aumouvantsillage/midi314/software/pcd8544/src/terminus6x12.rs

use font::*;

pub const WIDTH : usize = 6;

pub const HEIGHT : usize = 12;

pub const CHARS : usize = 892;

pub static BITMAP : [u8 ; CHARS * HEIGHT] = [
//   0 $00 'char0'
//	width 6, bbx 0, bby -2, bbw 6, bbh 12
	________,
	________,
	XX_XX___,
	X___X___,
	________,
	X___X___,
	X___X___,
	________,
	X___X___,
	XX_XX___,
	________,
	________,
//  32 $20 'space'
//	width 6, bbx 0, bby -2, bbw 6, bbh 12
	________,
	________,
	________,
	________,
	________,
	________,
	________,
	________,
	________,
	________,
	________,
	________,
//  33 $21 'exclam'
//	width 6, bbx 0, bby -2, bbw 6, bbh 12
	________,
	________,
	__X_____,
	__X_____,
	__X_____,
	__X_____,
	__X_____,
	________,
	__X_____,
	__X_____,
	________,
	________,
//  34 $22 'quotedbl'
//	width 6, bbx 0, bby -2, bbw 6, bbh 12
	________,
	_X_X____,
	_X_X____,
	_X_X____,
	________,
	________,
	________,
	________,
	________,
	________,
	________,
	________,
//  35 $23 'numbersign'
//	width 6, bbx 0, bby -2, bbw 6, bbh 12
	________,
	________,
	_X_X____,
	_X_X____,
	XXXXX___,
	_X_X____,
	_X_X____,
	XXXXX___,
	_X_X____,
	_X_X____,
	________,
	________,
//  36 $24 'dollar'
//	width 6, bbx 0, bby -2, bbw 6, bbh 12
	________,
	________,
	__X_____,
	_XXX____,
	X_X_X___,
	X_X_____,
	_XXX____,
	__X_X___,
	X_X_X___,
	_XXX____,
	__X_____,
	________,
//  37 $25 'percent'
//	width 6, bbx 0, bby -2, bbw 6, bbh 12
	________,
	________,
	_X__X___,
	X_X_X___,
	_X_X____,
	___X____,
	__X_____,
	__X_X___,
	_X_X_X__,
	_X__X___,
	________,
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
//	width 6, bbx 0, bby -2, bbw 6, bbh 12
	________,
	________,
	__X_X___,
	_X_X____,
	X___X___,
	X___X___,
	X___X___,
	X___X___,
	X___X___,
	_XXXX___,
	____X___,
	_XXX____,
// 8192 $2000 'uni2000'
//	width 6, bbx 0, bby -2, bbw 6, bbh 12
	________,
	________,
	________,
	________,
	________,
	________,
	________,
	________,
	________,
	________,
	________,
	________,
// 8193 $2001 'uni2001'
//	width 6, bbx 0, bby -2, bbw 6, bbh 12
	________,
	________,
	________,
	________,
	________,
	________,
	________,
	________,
	________,
	________,
	________,
	________,
// 8194 $2002 'enspace'
//	width 6, bbx 0, bby -2, bbw 6, bbh 12
	________,
	________,
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
