aumouvantsillage/midi314/software/pcd8544/src/font.rs

pub const ________ : u8 = 0x00;
pub const _______X : u8 = 0x01;
pub const ______X_ : u8 = 0x02;
pub const ______XX : u8 = 0x03;
pub const _____X__ : u8 = 0x04;
pub const _____X_X : u8 = 0x05;
pub const _____XX_ : u8 = 0x06;
pub const _____XXX : u8 = 0x07;
pub const ____X___ : u8 = 0x08;
pub const ____X__X : u8 = 0x09;
pub const ____X_X_ : u8 = 0x0A;
pub const ____X_XX : u8 = 0x0B;
pub const ____XX__ : u8 = 0x0C;
pub const ____XX_X : u8 = 0x0D;
pub const ____XXX_ : u8 = 0x0E;
pub const ____XXXX : u8 = 0x0F;
pub const ___X____ : u8 = 0x10;
pub const ___X___X : u8 = 0x11;
pub const ___X__X_ : u8 = 0x12;
pub const ___X__XX : u8 = 0x13;
pub const ___X_X__ : u8 = 0x14;
pub const ___X_X_X : u8 = 0x15;
pub const ___X_XX_ : u8 = 0x16;
pub const ___X_XXX : u8 = 0x17;
pub const ___XX___ : u8 = 0x18;
pub const ___XX__X : u8 = 0x19;
pub const ___XX_X_ : u8 = 0x1A;
pub const ___XX_XX : u8 = 0x1B;
pub const ___XXX__ : u8 = 0x1C;
pub const ___XXX_X : u8 = 0x1D;
pub const ___XXXX_ : u8 = 0x1E;
pub const ___XXXXX : u8 = 0x1F;
pub const __X_____ : u8 = 0x20;
pub const __X____X : u8 = 0x21;
pub const __X___X_ : u8 = 0x22;
pub const __X___XX : u8 = 0x23;
pub const __X__X__ : u8 = 0x24;
pub const __X__X_X : u8 = 0x25;
pub const __X__XX_ : u8 = 0x26;
pub const __X__XXX : u8 = 0x27;
pub const __X_X___ : u8 = 0x28;
pub const __X_X__X : u8 = 0x29;
pub const __X_X_X_ : u8 = 0x2A;
pub const __X_X_XX : u8 = 0x2B;
pub const __X_XX__ : u8 = 0x2C;
pub const __X_XX_X : u8 = 0x2D;
pub const __X_XXX_ : u8 = 0x2E;
pub const __X_XXXX : u8 = 0x2F;
pub const __XX____ : u8 = 0x30;
pub const __XX___X : u8 = 0x31;
pub const __XX__X_ : u8 = 0x32;
pub const __XX__XX : u8 = 0x33;
pub const __XX_X__ : u8 = 0x34;
pub const __XX_X_X : u8 = 0x35;
pub const __XX_XX_ : u8 = 0x36;
pub const __XX_XXX : u8 = 0x37;
pub const __XXX___ : u8 = 0x38;
pub const __XXX__X : u8 = 0x39;
pub const __XXX_X_ : u8 = 0x3A;
pub const __XXX_XX : u8 = 0x3B;
pub const __XXXX__ : u8 = 0x3C;
pub const __XXXX_X : u8 = 0x3D;
pub const __XXXXX_ : u8 = 0x3E;
pub const __XXXXXX : u8 = 0x3F;
pub const _X______ : u8 = 0x40;
pub const _X_____X : u8 = 0x41;
pub const _X____X_ : u8 = 0x42;
pub const _X____XX : u8 = 0x43;
pub const _X___X__ : u8 = 0x44;
pub const _X___X_X : u8 = 0x45;
pub const _X___XX_ : u8 = 0x46;
pub const _X___XXX : u8 = 0x47;
pub const _X__X___ : u8 = 0x48;
pub const _X__X__X : u8 = 0x49;
pub const _X__X_X_ : u8 = 0x4A;
pub const _X__X_XX : u8 = 0x4B;
pub const _X__XX__ : u8 = 0x4C;
pub const _X__XX_X : u8 = 0x4D;
pub const _X__XXX_ : u8 = 0x4E;
pub const _X__XXXX : u8 = 0x4F;
pub const _X_X____ : u8 = 0x50;
pub const _X_X___X : u8 = 0x51;
pub const _X_X__X_ : u8 = 0x52;
pub const _X_X__XX : u8 = 0x53;
pub const _X_X_X__ : u8 = 0x54;
pub const _X_X_X_X : u8 = 0x55;
pub const _X_X_XX_ : u8 = 0x56;
pub const _X_X_XXX : u8 = 0x57;
pub const _X_XX___ : u8 = 0x58;
pub const _X_XX__X : u8 = 0x59;
pub const _X_XX_X_ : u8 = 0x5A;
pub const _X_XX_XX : u8 = 0x5B;
pub const _X_XXX__ : u8 = 0x5C;
pub const _X_XXX_X : u8 = 0x5D;
pub const _X_XXXX_ : u8 = 0x5E;
pub const _X_XXXXX : u8 = 0x5F;
pub const _XX_____ : u8 = 0x60;
pub const _XX____X : u8 = 0x61;
pub const _XX___X_ : u8 = 0x62;
pub const _XX___XX : u8 = 0x63;
pub const _XX__X__ : u8 = 0x64;
pub const _XX__X_X : u8 = 0x65;
pub const _XX__XX_ : u8 = 0x66;
pub const _XX__XXX : u8 = 0x67;
pub const _XX_X___ : u8 = 0x68;
pub const _XX_X__X : u8 = 0x69;
pub const _XX_X_X_ : u8 = 0x6A;
pub const _XX_X_XX : u8 = 0x6B;
pub const _XX_XX__ : u8 = 0x6C;
pub const _XX_XX_X : u8 = 0x6D;
pub const _XX_XXX_ : u8 = 0x6E;
pub const _XX_XXXX : u8 = 0x6F;
pub const _XXX____ : u8 = 0x70;
pub const _XXX___X : u8 = 0x71;
pub const _XXX__X_ : u8 = 0x72;
pub const _XXX__XX : u8 = 0x73;
pub const _XXX_X__ : u8 = 0x74;
pub const _XXX_X_X : u8 = 0x75;
pub const _XXX_XX_ : u8 = 0x76;
pub const _XXX_XXX : u8 = 0x77;
pub const _XXXX___ : u8 = 0x78;
pub const _XXXX__X : u8 = 0x79;
pub const _XXXX_X_ : u8 = 0x7A;
pub const _XXXX_XX : u8 = 0x7B;
pub const _XXXXX__ : u8 = 0x7C;
pub const _XXXXX_X : u8 = 0x7D;
pub const _XXXXXX_ : u8 = 0x7E;
pub const _XXXXXXX : u8 = 0x7F;
pub const X_______ : u8 = 0x80;
pub const X______X : u8 = 0x81;
pub const X_____X_ : u8 = 0x82;
pub const X_____XX : u8 = 0x83;
pub const X____X__ : u8 = 0x84;
pub const X____X_X : u8 = 0x85;
pub const X____XX_ : u8 = 0x86;
pub const X____XXX : u8 = 0x87;
pub const X___X___ : u8 = 0x88;
pub const X___X__X : u8 = 0x89;
pub const X___X_X_ : u8 = 0x8A;
pub const X___X_XX : u8 = 0x8B;
pub const X___XX__ : u8 = 0x8C;
pub const X___XX_X : u8 = 0x8D;
pub const X___XXX_ : u8 = 0x8E;
pub const X___XXXX : u8 = 0x8F;
pub const X__X____ : u8 = 0x90;
pub const X__X___X : u8 = 0x91;
pub const X__X__X_ : u8 = 0x92;
pub const X__X__XX : u8 = 0x93;
pub const X__X_X__ : u8 = 0x94;
pub const X__X_X_X : u8 = 0x95;
pub const X__X_XX_ : u8 = 0x96;
pub const X__X_XXX : u8 = 0x97;
pub const X__XX___ : u8 = 0x98;
pub const X__XX__X : u8 = 0x99;
pub const X__XX_X_ : u8 = 0x9A;
pub const X__XX_XX : u8 = 0x9B;
pub const X__XXX__ : u8 = 0x9C;
pub const X__XXX_X : u8 = 0x9D;
pub const X__XXXX_ : u8 = 0x9E;
pub const X__XXXXX : u8 = 0x9F;
pub const X_X_____ : u8 = 0xA0;
pub const X_X____X : u8 = 0xA1;
pub const X_X___X_ : u8 = 0xA2;
pub const X_X___XX : u8 = 0xA3;
pub const X_X__X__ : u8 = 0xA4;
pub const X_X__X_X : u8 = 0xA5;
pub const X_X__XX_ : u8 = 0xA6;
pub const X_X__XXX : u8 = 0xA7;
pub const X_X_X___ : u8 = 0xA8;
pub const X_X_X__X : u8 = 0xA9;
pub const X_X_X_X_ : u8 = 0xAA;
pub const X_X_X_XX : u8 = 0xAB;
pub const X_X_XX__ : u8 = 0xAC;
pub const X_X_XX_X : u8 = 0xAD;
pub const X_X_XXX_ : u8 = 0xAE;
pub const X_X_XXXX : u8 = 0xAF;
pub const X_XX____ : u8 = 0xB0;
pub const X_XX___X : u8 = 0xB1;
pub const X_XX__X_ : u8 = 0xB2;
pub const X_XX__XX : u8 = 0xB3;
pub const X_XX_X__ : u8 = 0xB4;
pub const X_XX_X_X : u8 = 0xB5;
pub const X_XX_XX_ : u8 = 0xB6;
pub const X_XX_XXX : u8 = 0xB7;
pub const X_XXX___ : u8 = 0xB8;
pub const X_XXX__X : u8 = 0xB9;
pub const X_XXX_X_ : u8 = 0xBA;
pub const X_XXX_XX : u8 = 0xBB;
pub const X_XXXX__ : u8 = 0xBC;
pub const X_XXXX_X : u8 = 0xBD;
pub const X_XXXXX_ : u8 = 0xBE;
pub const X_XXXXXX : u8 = 0xBF;
pub const XX______ : u8 = 0xC0;
pub const XX_____X : u8 = 0xC1;
pub const XX____X_ : u8 = 0xC2;
pub const XX____XX : u8 = 0xC3;
pub const XX___X__ : u8 = 0xC4;
pub const XX___X_X : u8 = 0xC5;
pub const XX___XX_ : u8 = 0xC6;
pub const XX___XXX : u8 = 0xC7;
pub const XX__X___ : u8 = 0xC8;
pub const XX__X__X : u8 = 0xC9;
pub const XX__X_X_ : u8 = 0xCA;
pub const XX__X_XX : u8 = 0xCB;
pub const XX__XX__ : u8 = 0xCC;
pub const XX__XX_X : u8 = 0xCD;
pub const XX__XXX_ : u8 = 0xCE;
pub const XX__XXXX : u8 = 0xCF;
pub const XX_X____ : u8 = 0xD0;
pub const XX_X___X : u8 = 0xD1;
pub const XX_X__X_ : u8 = 0xD2;
pub const XX_X__XX : u8 = 0xD3;
pub const XX_X_X__ : u8 = 0xD4;
pub const XX_X_X_X : u8 = 0xD5;
pub const XX_X_XX_ : u8 = 0xD6;
pub const XX_X_XXX : u8 = 0xD7;
pub const XX_XX___ : u8 = 0xD8;
pub const XX_XX__X : u8 = 0xD9;
pub const XX_XX_X_ : u8 = 0xDA;
pub const XX_XX_XX : u8 = 0xDB;
pub const XX_XXX__ : u8 = 0xDC;
pub const XX_XXX_X : u8 = 0xDD;
pub const XX_XXXX_ : u8 = 0xDE;
pub const XX_XXXXX : u8 = 0xDF;
pub const XXX_____ : u8 = 0xE0;
pub const XXX____X : u8 = 0xE1;
pub const XXX___X_ : u8 = 0xE2;
pub const XXX___XX : u8 = 0xE3;
pub const XXX__X__ : u8 = 0xE4;
pub const XXX__X_X : u8 = 0xE5;
pub const XXX__XX_ : u8 = 0xE6;
pub const XXX__XXX : u8 = 0xE7;
pub const XXX_X___ : u8 = 0xE8;
pub const XXX_X__X : u8 = 0xE9;
pub const XXX_X_X_ : u8 = 0xEA;
pub const XXX_X_XX : u8 = 0xEB;
pub const XXX_XX__ : u8 = 0xEC;
pub const XXX_XX_X : u8 = 0xED;
pub const XXX_XXX_ : u8 = 0xEE;
pub const XXX_XXXX : u8 = 0xEF;
pub const XXXX____ : u8 = 0xF0;
pub const XXXX___X : u8 = 0xF1;
pub const XXXX__X_ : u8 = 0xF2;
pub const XXXX__XX : u8 = 0xF3;
pub const XXXX_X__ : u8 = 0xF4;
pub const XXXX_X_X : u8 = 0xF5;
pub const XXXX_XX_ : u8 = 0xF6;
pub const XXXX_XXX : u8 = 0xF7;
pub const XXXXX___ : u8 = 0xF8;
pub const XXXXX__X : u8 = 0xF9;
pub const XXXXX_X_ : u8 = 0xFA;
pub const XXXXX_XX : u8 = 0xFB;
pub const XXXXXX__ : u8 = 0xFC;
pub const XXXXXX_X : u8 = 0xFD;
pub const XXXXXXX_ : u8 = 0xFE;
pub const XXXXXXXX : u8 = 0xFF;
